Dreambrother7/FZ1oledlc/pcb/deftaudio_pico_oled/Pico_FZ1_OLED_PCB.kicad_sch

## KiCad design pcb/deftaudio_pico_oled/Pico_FZ1_OLED_PCB.kicad_sch (2026-06-28)

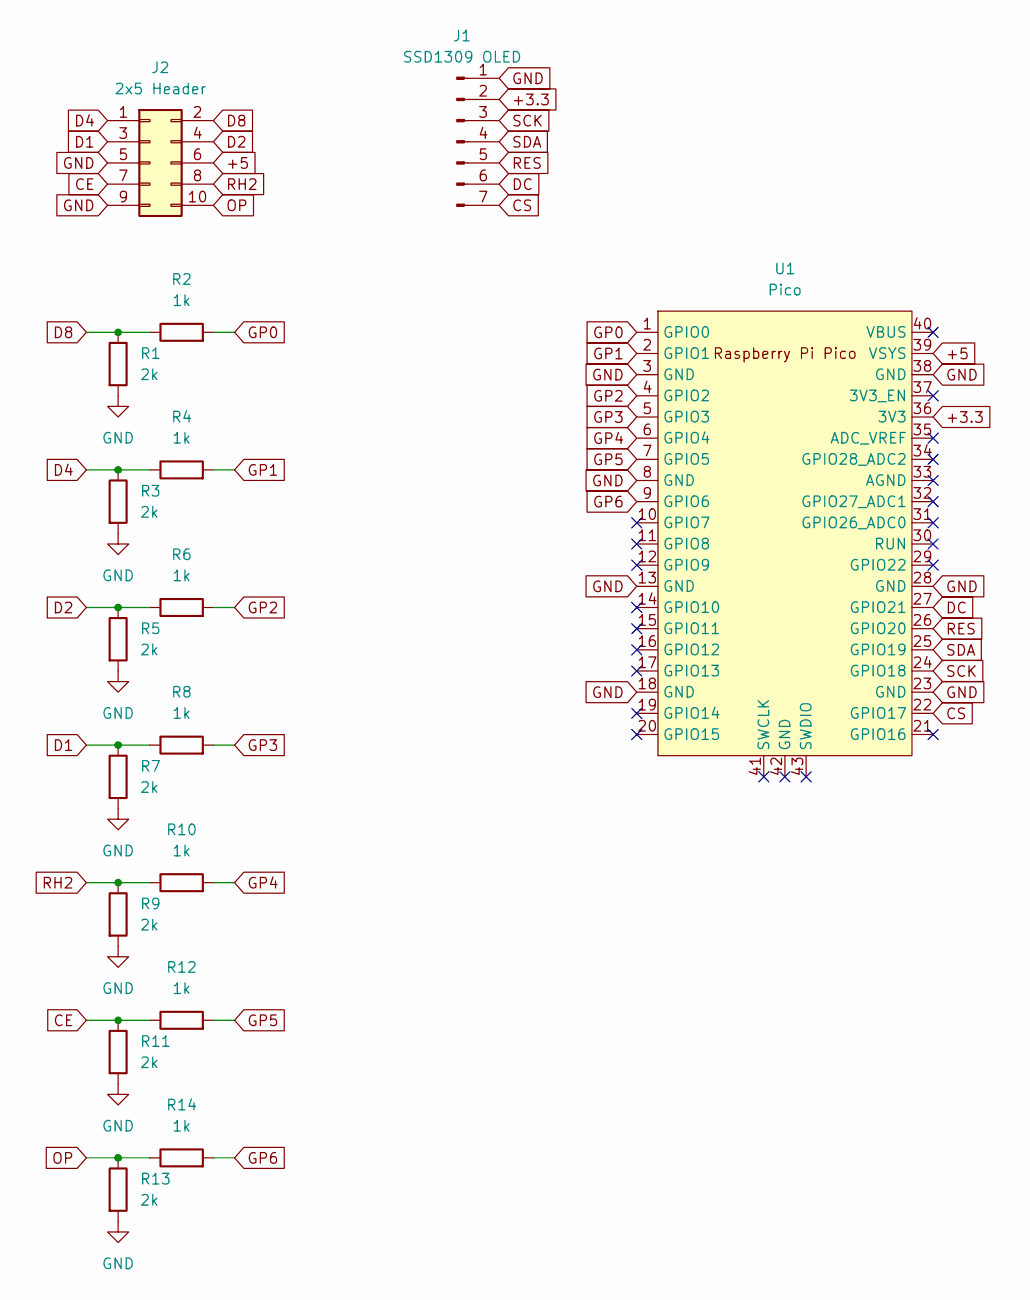
[picture p7: schematic Pico_FZ1_OLED_PCB.kicad_sch]

Parts:
J1: SSD1309 OLED; PinHeader_1x07_P2.54mm_Vertical
J2: 2x5 Header; PinHeader_2x05_P2.00mm_Vertical
R1, R3, R5, R7, R9, R11, R13: 2k; R_Axial_DIN0207_L6.3mm_D2.5mm_P7.62mm_Horizontal
R2, R4, R6, R8, R10, R12, R14: 1k; R_Axial_DIN0207_L6.3mm_D2.5mm_P7.62mm_Horizontal
U1: Pico; RaspberryPi_Pico_Common_Unspecified

Connections:
+3.3: J1.2, U1.36 (3V3)
+5: J2.6, U1.39 (VSYS)
CE: J2.7, R11.1, R12.1
CS: J1.7, U1.22 (GPIO17)
D1: J2.3, R7.1, R8.1
D2: J2.4, R5.1, R6.1
D4: J2.1, R3.1, R4.1
D8: J2.2, R1.1, R2.1
DC: J1.6, U1.27 (GPIO21)
GND: J1.1, J2.5, J2.9, R1.2, R3.2, R5.2, R7.2, R9.2, R11.2, R13.2, U1.3 (GND), U1.8 (GND), U1.13 (GND), U1.18 (GND), U1.23 (GND), U1.28 (GND), U1.38 (GND)
GP0: R2.2, U1.1 (GPIO0)
GP1: R4.2, U1.2 (GPIO1)
GP2: R6.2, U1.4 (GPIO2)
GP3: R8.2, U1.5 (GPIO3)
GP4: R10.2, U1.6 (GPIO4)
GP5: R12.2, U1.7 (GPIO5)
GP6: R14.2, U1.9 (GPIO6)
OP: J2.10, R13.1, R14.1
RES: J1.5, U1.26 (GPIO20)
RH2: J2.8, R9.1, R10.1
SCK: J1.3, U1.24 (GPIO18)
SDA: J1.4, U1.25 (GPIO19)
