Dreambrother7/FZ1oledlc/pcb/deftaudio_connector_adapters/fz1_oled_IDC_adapter_v2/fz1_oled_IDC_adapter.kicad_sch

## KiCad design pcb/deftaudio_connector_adapters/fz1_oled_IDC_adapter_v2/fz1_oled_IDC_adapter.kicad_sch (2026-06-28)

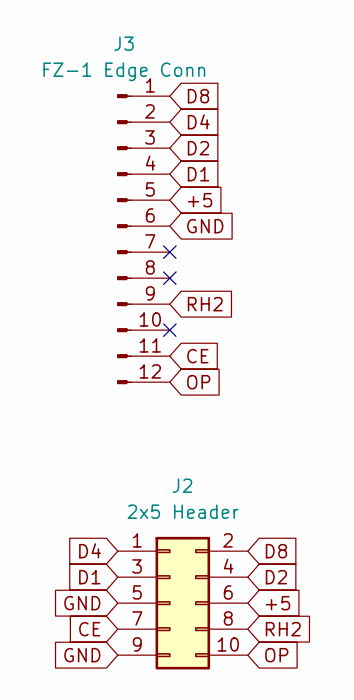
[picture p8: schematic fz1_oled_IDC_adapter.kicad_sch]

Parts:
J2: 2x5 Header; PinHeader_2x05_P2.00mm_Vertical
J3: FZ-1 Edge Conn; fz1

Connections:
+5: J2.6, J3.5
CE: J2.7, J3.11
D1: J2.3, J3.4
D2: J2.4, J3.3
D4: J2.1, J3.2
D8: J2.2, J3.1
GND: J2.5, J2.9, J3.6
OP: J2.10, J3.12
RH2: J2.8, J3.9
