Dreambrother7/FZ1oledlc/pcb/deftaudio_connector_adapters/fz10m_fz20m_vz10m_oled_IDC_adapter/fz10_oled_IDC_adapter.kicad_sch

## KiCad design pcb/deftaudio_connector_adapters/fz10m_fz20m_vz10m_oled_IDC_adapter/fz10_oled_IDC_adapter.kicad_sch (2026-06-28)

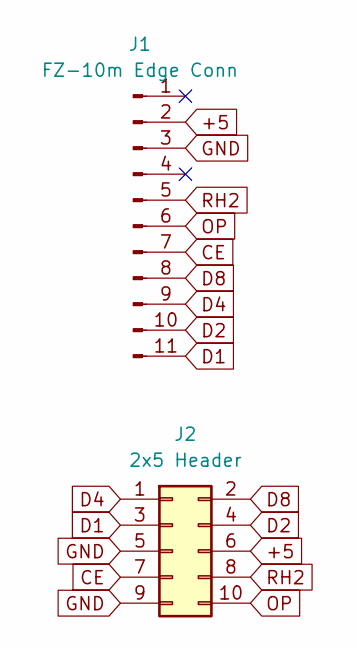
[picture p9: schematic fz10_oled_IDC_adapter.kicad_sch]

Parts:
J1: FZ-10m Edge Conn; fz10m
J2: 2x5 Header; PinHeader_2x05_P2.00mm_Vertical

Connections:
+5: J1.2, J2.6
CE: J1.7, J2.7
D1: J1.11, J2.3
D2: J1.10, J2.4
D4: J1.9, J2.1
D8: J1.8, J2.2
GND: J1.3, J2.5, J2.9
OP: J1.6, J2.10
RH2: J1.5, J2.8
